Phunkafizer/OT-Thing/Firmware/include/sensors.h

#pragma once

#include <Arduino.h>
#include <ArduinoJson.h>
#include <AsyncTCP.h>
#include <OneWire.h>
#include <NimBLEDevice.h>
#include <vector>
#include "util.h"

class AddressableSensor {
friend class Sensor;
friend class SensorLock;
private:
    uint8_t adrLen;
    static SemaphoreHandle_t mutex;
protected:
    AddressableSensor(const uint8_t *adr, const uint8_t adrLen, AddressableSensor **prev);
    String getAdr() const;
    static AddressableSensor* find(String adr, AddressableSensor *last);
    static void writeJsonAll(JsonObject &status, AddressableSensor *last);
    virtual void writeJson(JsonVariant val) = 0;
    static bool sendDiscoveryAll(AddressableSensor *last);
    virtual bool sendDiscovery() = 0;
    uint8_t adr[8];
    AddressableSensor *next;
    double temp;
public:
    static void begin();
};

class BLESensor: public AddressableSensor {
private:
    void parse(std::string &data);
    static BLESensor *last;
    uint8_t rh;
    uint8_t bat;
    int8_t rssi;
protected:
    void writeJson(JsonVariant val) override;
    bool sendDiscovery() override;
public:
    BLESensor(const uint8_t *adr);
    static void begin();
    static void onDiscovery(const NimBLEAdvertisedDevice* dev);
    static void writeJsonAll(JsonObject &status);
    static BLESensor* find(const uint8_t *adr);
    static bool sendDiscoveryAll();
};

class OneWireNode: public AddressableSensor {
private:
    static OneWireNode *last;
protected:
    void writeJson(JsonVariant val) override;
    bool sendDiscovery() override;
public:
    OneWireNode(uint8_t *addr);
    virtual ~OneWireNode() {}
    static void begin(const uint8_t gpio);
    static void clear();
    static OneWireNode* find(String adr);
    static void loop();
    static void writeJsonAll(JsonObject &status);
    static bool sendDiscoveryAll();
};

class Sensor {
public:
    enum Source: int8_t {
        SOURCE_SCHED = -3,
        SOURCE_HTTP = -2,
        SOURCE_NA = -1,
        SOURCE_MQTT = 0,
        SOURCE_OT = 1,
        SOURCE_BLE = 2,
        SOURCE_1WIRE = 3,
        SOURCE_OPENWEATHER = 4,
        SOURCE_AUTO = 5 // has to be last item in this list!
    };
    Source lastSetSrc {SOURCE_NA};
    OneWireNode *own; // points to a OneWireNode if configured
    Sensor(const double alpha);
    virtual void set(const double val, const Source src, const Source lastSrc = SOURCE_NA);
    bool get(double &val, const bool raw = false);
    virtual void writeJson(JsonVariant val);
    virtual void setConfig(JsonObject &obj);
    bool isMqttSource();
    bool isOtSource();
    static void loopAll();
    explicit operator bool() const;
    static std::vector<Sensor*> findByOwn(const OneWireNode *own);
protected:
    Source src;
    double value;
    double smoothed;
    bool setFlag;
    virtual void loop() {}
private:
    void updateSmooth();
    static uint32_t lastSmooth;
    static Sensor *lastSensor;
    Sensor *prevSensor;
    uint8_t adr[6];
    double alpha;
};

class AutoSensor: public Sensor {
public:
    AutoSensor();
    void set(const double val, const Source src, const Source lastSrc = SOURCE_NA) override;
private:
    double values[SOURCE_AUTO + 1];
};

class OutsideTemp: public Sensor {
public:
    String owResult;
    OutsideTemp();
    void setConfig(JsonObject &obj) override;
    void set(const double val, const Source src, const Source lastSrc = SOURCE_NA) override;
    void writeJson(JsonVariant val) override;
    double getAvg() const;
protected:
    void loop() override;
private:
    uint32_t nextMillis;
    uint32_t interval;
    double lat, lon;
    String apikey;
    AsyncClient acli;
    String replyBuf;
    enum {
        HTTP_IDLE,
        HTTP_CONNECTING,
        HTTP_RECEIVING
    } httpState;
    double minValues[24];
    double maxValues[24];
    int lastHistPos {-1};
};

extern Sensor roomTemp[2];
extern AutoSensor roomSetPoint[2];
extern OutsideTemp outsideTemp;
extern Sensor returnTemp[2];
