Phunkafizer/OT-Thing/Firmware/src/mqtt.cpp

#include "mqtt.h"
#include <WiFi.h>
#include <devstatus.h>
#include "portal.h"
#include "sensors.h"
#include "hwdef.h"
#include "auxInput.h"
#include "otcontrol.h"
#include "util.h"

static struct {
    Mqtt::MqttTopic topic;
    const char *str;
} topicList[] PROGMEM = {
    {Mqtt::TOPIC_OUTSIDETEMP, "outsideTemp"},
    {Mqtt::TOPIC_DHWSETTEMP, "dhwSetTemp"},
    {Mqtt::TOPIC_CHSETTEMP1, "chSetTemp1"},
    {Mqtt::TOPIC_CHSETTEMP2, "chSetTemp2"},
    {Mqtt::TOPIC_CHMINTEMP1, "chMinTemp1"},
    {Mqtt::TOPIC_CHMINTEMP2, "chMinTemp2"},
    {Mqtt::TOPIC_DHWMODE, "dhwMode"},
    {Mqtt::TOPIC_CHMODE1, "chMode1"},
    {Mqtt::TOPIC_CHMODE2, "chMode2"},
    {Mqtt::TOPIC_ROOMTEMP1, "roomTemp1"},
    {Mqtt::TOPIC_ROOMTEMP2, "roomTemp2"},
    {Mqtt::TOPIC_ROOMMODE1, "roomMode1"},
    {Mqtt::TOPIC_ROOMMODE2, "roomMode2"},
    {Mqtt::TOPIC_ROOMSETPOINT1, "roomSetpoint1"},
    {Mqtt::TOPIC_ROOMSETPOINT2, "roomSetpoint2"},
    {Mqtt::TOPIC_OVERRIDECHFLOW1, "overrideChFlow1"},
    {Mqtt::TOPIC_OVERRIDECHFLOW2, "overrideChFlow2"},
    {Mqtt::TOPIC_OVERRIDECHON1, "overrideChOn1"},
    {Mqtt::TOPIC_OVERRIDECHON2, "overrideChOn2"},
    {Mqtt::TOPIC_VENTSETPOINT, "ventSetpoint"},
    {Mqtt::TOPIC_VENTENABLE, "ventEnable"},
    {Mqtt::TOPIC_OPENBYPASS, "openBypass"},
    {Mqtt::TOPIC_AUTOBYPASS, "autoBypass"},
    {Mqtt::TOPIC_FREEVENTENABLE, "freeVentEnable"},
    {Mqtt::TOPIC_MAXMODULATION, "maxModulation"},
    {Mqtt::TOPIC_BYPASS, "bypass"},
    {Mqtt::TOPIC_SUMMERMODE, "summerMode"},
    {Mqtt::TOPIC_DHWBLOCKING, "dhwBlocking"},
    {Mqtt::TOPIC_COOLINGMODE, "coolingMode"},
    {Mqtt::TOPIC_COOLINGCTRL, "coolingCtrl"},
    {Mqtt::TOPIC_TURBOSHIFT1, "turboShift1"},
    {Mqtt::TOPIC_TURBOSHIFT2, "turboShift2"},
    {Mqtt::TOPIC_TURBODURATION1, "turboDuration1"},
    {Mqtt::TOPIC_TURBODURATION2, "turboDuration2"},
};

Mqtt mqtt;
static uint32_t numDisc = 0;
static WiFiClient espClient;
static String mqttRxTopic;
static String mqttRxPayload;

void mqttConnectCb(bool sessionPresent) {
    mqtt.onConnect();
}

void mqttDisconnectCb(AsyncMqttClientDisconnectReason reason) {
    mqtt.onDisconnect(reason);
}

static void mqttMessageReceived(char* topic, char* payload, AsyncMqttClientMessageProperties properties, size_t len, size_t index, size_t total) {
    // AsyncMqttClient may deliver one MQTT message in multiple chunks.
    if (index == 0) {
        mqttRxTopic = String(topic);
        mqttRxPayload = "";
        mqttRxPayload.reserve(total);
    }

    if (mqttRxTopic != String(topic)) {
        mqttRxTopic = String(topic);
        mqttRxPayload = "";
        mqttRxPayload.reserve(total);
    }

    mqttRxPayload.concat(payload, len);

    if ((index + len) >= total) {
        mqtt.onMessage(topic, mqttRxPayload);
        mqttRxTopic = "";
        mqttRxPayload = "";
    }
}

Mqtt::Mqtt():
        lastConTry(0),
        lastStatus(0),
        configSet(false),
        conFlag(false),
        lastSentStatus(0) {
    cli.onConnect(mqttConnectCb);
    cli.onDisconnect(mqttDisconnectCb);
    cli.onMessage(mqttMessageReceived);
}

void Mqtt::begin() {
    String shortMac = getShortMac();
    baseTopic = F("otthing/");
    baseTopic += shortMac;
    statusTopic = baseTopic + F("/status");
}

void Mqtt::onConnect() {
    portal.textAll(F("MQTT connected"));

    String topic = baseTopic + F("/+/set");
    cli.subscribe(topic.c_str(), 0);

    discFlag = false;
    conFlag = true;
}

void Mqtt::onDisconnect(AsyncMqttClientDisconnectReason reason) {
    if (conFlag) {
        String msg = F("MQTT disconnected ");
        msg += String((int) reason);
        portal.textAll(msg);
        conFlag = false;
        numDisc++;
    }
}

bool Mqtt::connected() {
    return cli.connected();
}

void Mqtt::setConfig(const MqttConfig conf) {
    lastConTry = millis() - 8000;
    cli.disconnect(false);
    config = conf;
    cli.setServer(config.host.c_str(), conf.port);
    cli.setKeepAlive(config.keepAlive);
    cli.setCredentials(config.user.c_str(), config.pass.c_str());
    configSet = !conf.host.isEmpty();
    numDisc = 0;
}

uint32_t Mqtt::getNumDisc() const {
    return numDisc;
}

String Mqtt::getCmdTopic(const MqttTopic topic) {
    String result = baseTopic + '/';
    result += getTopicString(topic);
    result += "/set";
    return result;
}

String Mqtt::getBaseTopic() {
    return baseTopic;
}

void Mqtt::loop() {
    if (!cli.connected() && ((millis() - lastConTry) > 10000) && WiFi.isConnected() && configSet) {
        lastConTry = millis();
        haDisc.defaultStateTopic = baseTopic + F("/state");
        cli.setWill(statusTopic.c_str(), 0, true, "0");
        lastSentStatus = 0;
        cli.connect();        
    }

    if (cli.connected()) {
        if (!discFlag) {
            discFlag = true;
            discFlag &= otcontrol.sendDiscovery();
            discFlag &= OneWireNode::sendDiscoveryAll();
            discFlag &= BLESensor::sendDiscoveryAll();
            for (int i=0; i<sizeof(auxInput) / sizeof(auxInput[0]); i++)
                discFlag &= auxInput[i].sendDiscovery();
        }

        int newStatus = 1 << 0;
        if (otcontrol.masterConnected())
            newStatus |= 1 << 1;
        if (otcontrol.slaveConnected())
            newStatus |= 1 << 2;
        if (newStatus != lastSentStatus) {
            lastSentStatus = newStatus;
            cli.publish(statusTopic.c_str(), 0, true, String(newStatus).c_str());
        }

        if ((millis() - lastStatus) > 5000) {
            lastStatus = millis();
            JsonDocument doc;
            JsonObject jobj = doc.to<JsonObject>();
            devstatus.buildDoc(jobj);
            String statStr;
            serializeJson(jobj, statStr);
            cli.publish(haDisc.defaultStateTopic.c_str(), 0, false, statStr.c_str());
        }
    }
}

bool Mqtt::strToBool(const String &str) {
    return str.compareTo(F("ON")) == 0;
}

bool Mqtt::publish(String topic, JsonDocument &payload, const bool retain) {
    if (!cli.connected())
        return false;

    String ps;
    if (!payload.isNull())
        serializeJson(payload, ps);
    cli.publish(topic.c_str(), 0, retain, ps.c_str());
    return true;
}

void Mqtt::onMessage(const char *topic, String &payload) {
    String topicStr = topic;
    topicStr.remove(0, baseTopic.length() + 1);
    topicStr.remove(topicStr.length() - 4, 4); // remove "/set" from end of topic

    String log = F("MQTT: ");
    log += topic;
    log += " ";
    log += payload;
    portal.textAll(log);

    if (setValue(topicStr, payload)) {
        if ((millis() - lastStatus) < 4500)
            lastStatus = millis() - 4500;
    }
}

bool Mqtt::setValue(const String &key, const String &value, const bool viaHttp) {
    enum MqttTopic etop = TOPIC_UNKNOWN;
    for (int i=0; i<sizeof(topicList) / sizeof(topicList[0]); i++)
        if (key.compareTo(FPSTR(topicList[i].str)) == 0) {
            etop = topicList[i].topic;
            break;
        }

    const Sensor::Source lastSrc = viaHttp ? Sensor::SOURCE_HTTP : Sensor::SOURCE_MQTT;
    bool retain = true;

    switch (etop) {
    case TOPIC_UNKNOWN: {
        String log = F("MQTT unknown topic: ");
        log += key;
        portal.textAll(log);
        return false;
    }

    case TOPIC_OUTSIDETEMP: {
        double d = value.toFloat();
        outsideTemp.set(d, Sensor::SOURCE_MQTT, lastSrc);
        break;
    }

    case TOPIC_DHWSETTEMP: {
        double d = value.toFloat();
        otcontrol.dhwControl.setSetpoint(d, lastSrc);
        break;
    }   

    case TOPIC_DHWMODE: {
        auto mode = haDisc.strToClimateMode(value);
        if (mode != HADiscovery::MODE_UNKNOWN)
            otcontrol.setDhwCtrlMode(mode);
        break;
    }

    case TOPIC_CHSETTEMP1:
    case TOPIC_CHSETTEMP2: {
        double d = value.toFloat();
        otcontrol.setChTemp(d, (uint8_t) (etop - TOPIC_CHSETTEMP1), lastSrc);
        break;
    }

    case TOPIC_CHMINTEMP1:
    case TOPIC_CHMINTEMP2: {
        double d = value.toFloat();
        otcontrol.setFlowMin(d, (uint8_t) (etop - TOPIC_CHMINTEMP1));
        break;
    }

    case TOPIC_CHMODE1:
    case TOPIC_CHMODE2: {
        const uint8_t ch = (uint8_t) (etop - TOPIC_CHMODE1);
        auto mode = haDisc.strToClimateMode(value);
        if (mode != HADiscovery::MODE_UNKNOWN)
            otcontrol.setChCtrlMode(mode, ch);
        break;
    }

    case TOPIC_ROOMTEMP1:
    case TOPIC_ROOMTEMP2: {
        const uint8_t ch = (uint8_t) (etop - TOPIC_ROOMTEMP1);
        double d = value.toFloat();
        roomTemp[ch].set(d, Sensor::SOURCE_MQTT, lastSrc);
        otcontrol.forceFlowCalc(ch);
        break;
    }

    case TOPIC_ROOMSETPOINT1:
    case TOPIC_ROOMSETPOINT2: {
        const uint8_t ch = (uint8_t) (etop - TOPIC_ROOMSETPOINT1);
        double d = value.toFloat();
        roomSetPoint[ch].set(d, Sensor::SOURCE_MQTT, lastSrc);
        otcontrol.forceFlowCalc(ch);
        break;
    }

    case TOPIC_ROOMMODE1:
    case TOPIC_ROOMMODE2: {
        auto mode = haDisc.strToClimateMode(value);
        if (mode != HADiscovery::MODE_UNKNOWN)
            otcontrol.setRoomMode(mode, (uint8_t) (etop - TOPIC_ROOMMODE1));
        break;
    }

    case TOPIC_OVERRIDECHON1:
    case TOPIC_OVERRIDECHON2:
        otcontrol.setOverrideChOn(strToBool(value), (uint8_t) (etop - TOPIC_OVERRIDECHON1));
        break;

    case TOPIC_OVERRIDECHFLOW1:
    case TOPIC_OVERRIDECHFLOW2:
        otcontrol.setOverrideChFlow(strToBool(value), (uint8_t) (etop - TOPIC_OVERRIDECHFLOW1));
        break;

    case TOPIC_VENTSETPOINT: {
        uint8_t val = value.toInt();
        otcontrol.ventCtrl.setVentSetpoint(val);
        break;
    }

    case TOPIC_VENTENABLE:
        otcontrol.ventCtrl.setVentEnable(strToBool(value));
        break;

    case TOPIC_OPENBYPASS:
        otcontrol.ventCtrl.setOpenBypass(strToBool(value));
        break;

    case TOPIC_AUTOBYPASS:
        otcontrol.ventCtrl.setAutoBypass(strToBool(value));
        break;

    case TOPIC_FREEVENTENABLE:
        otcontrol.ventCtrl.setFreeVentEnable(strToBool(value));
        break;

    case TOPIC_MAXMODULATION: {
        int i = value.toInt();
        otcontrol.setMaxMod(i);
        break;
    }

    case TOPIC_BYPASS:
        otcontrol.setBypass(strToBool(value));
        break;

    case TOPIC_SUMMERMODE:
        otcontrol.setSummerMode(strToBool(value));
        break;

    case TOPIC_DHWBLOCKING:
        otcontrol.setDhwBlocking(strToBool(value));
        break;

    case TOPIC_COOLINGMODE:
        otcontrol.setCoolingMode(strToBool(value));
        break;

    case TOPIC_COOLINGCTRL:
        otcontrol.setCoolingCtrl(value.toInt());
        break;

    case TOPIC_TURBOSHIFT1:
    case TOPIC_TURBOSHIFT2: {
        const uint8_t ch = (uint8_t) (etop - TOPIC_TURBOSHIFT1);
        double d = value.toFloat();
        otcontrol.setTurboShift(d, ch);
        retain = false;
        break;
    }

    case TOPIC_TURBODURATION1:
    case TOPIC_TURBODURATION2: {
        const uint8_t ch = (uint8_t) (etop - TOPIC_TURBODURATION1);
        uint32_t d = value.toInt();
        otcontrol.setTurboDuration(d, ch);
        retain = false;
        break;
    }

    default:
        return false;
    }

    if (viaHttp)
        sendValue(etop, value, retain);

    return true;
}

void Mqtt::sendValue(const MqttTopic topic, const String &value, const bool retain) {
    if (!connected())
        return;

    String topicStr = baseTopic + '/';
    topicStr += getTopicString(topic);
    topicStr += "/set";
    cli.publish(topicStr.c_str(), 0, retain, value.c_str());
}

String Mqtt::getTopicString(const MqttTopic topic) {
    for (int i=0; i<sizeof(topicList) / sizeof(topicList[0]); i++)
        if (topicList[i].topic == topic)
            return FPSTR(topicList[i].str);
    return "";
}

String Mqtt::getValuePath(const ValueTemplateType vt, PGM_P field, const uint8_t ch, const uint8_t ommit) {
    String result = F("{% set tmp=(((value_json");
    String ftmp = FPSTR(field); // e. g. "dhw_set_t", "status.dhw_enable"

    switch (vt) {
    case VALTMPL_NONE:
        return "";
        
    case VALTMPL_ROOT:
        result += F(")"); // result: {% set tmp=(((value_json)
        break;
        
    case VALTMPL_SLAVE:
        result += F(".get('slave') or {})"); // result: {% set tmp=(((value_json.get('slave') or {})
        break;

    case VALTMPL_MASTER: {
        const int pidx = ftmp.indexOf('.');
        if (pidx > -1)
            ftmp = ftmp.substring(0, pidx) + F(".data") + ftmp.substring(pidx); // adds 
        else
            ftmp += F(".data");
        [[fallthrough]];
    }

    case VALTMPL_MASTER_ROOT:
        result += F(".get('master') or {})"); // result: {% set tmp=(((value_json.get('master') or {})
        break;

    case VALTMPL_ROOMUNIT: {
        const int pidx = ftmp.indexOf('.');
        if (pidx > -1)
            ftmp = ftmp.substring(0, pidx) + F(".data") + ftmp.substring(pidx);
        else
            ftmp += F(".data");
        [[fallthrough]];
    }

    case VALTMPL_ROOMUNIT_ROOT:
        result += F(".get('roomunit') or {})");
        break;

    case VALTMPL_HEATING_CIRCUIT:
        result += F(".get('heatercircuit') or [])[#]");
        break;

    case VALTMPL_DHW:
        result += F(".get('dhw') or {})");
        break;

    case VALTMPL_FLAMESTATS:
        result += F(".get('slave') or {}).get('flameStats') or {}");
        break;

    case VALTMPL_COOLING:
        result += F(".get('cooling') or {})");
        break;

    case VALTMPL_VENT:
        result += F(".get('vent') or {})");
        break;
    }

    int numbrak = 2;

    while (true) {
        auto pidx = ftmp.indexOf('.');

        if (pidx > -1) {
            result += F(".get('");
            result += ftmp.substring(0, pidx);
            result += F("') or {})");
            ftmp.remove(0, pidx + 1);
            numbrak--;
        }
        else
            break;
    }
    for (int i=0; i<numbrak; i++)
        result += ')';

    result += F(".get('");
    result += ftmp;
    result += F("') %}");

    if (ch == ommit)
        result.replace("#", "");
    else
        result.replace("#", String(ch));

    return result;
}

String Mqtt::getValueTemplate(const ValueTemplateType vt, PGM_P field, const uint8_t ch, const uint8_t ommit) {
    String result = getValuePath(vt, field, ch, ommit);
    result += F("{{ tmp | default(none) }}");
    return result;
}

String Mqtt::getValueTemplateBool(const ValueTemplateType vt, PGM_P field, const uint8_t ch, const uint8_t ommit) {
    String result = getValuePath(vt, field, ch, ommit);
    result += F("{{ none if tmp is none else 'ON' if tmp else 'OFF' }}");
    return result;
}

String &Mqtt::getStatusTopic() {
    return statusTopic;
}
