Phunkafizer/OT-Thing/Firmware/include/mqtt.h

#pragma once

#include <AsyncMqttClient.h>
#include <ArduinoJson.h>

struct MqttConfig {
    String host;
    uint16_t port;
    bool tls;
    String user;
    String pass;
    uint16_t keepAlive;
};

class Mqtt {
public:
    enum MqttTopic: uint8_t {
        TOPIC_OUTSIDETEMP,
        TOPIC_DHWSETTEMP,
        TOPIC_CHSETTEMP1,
        TOPIC_CHSETTEMP2,
        TOPIC_CHMINTEMP1,
        TOPIC_CHMINTEMP2,
        TOPIC_DHWMODE,
        TOPIC_CHMODE1,
        TOPIC_CHMODE2,
        TOPIC_ROOMTEMP1,
        TOPIC_ROOMTEMP2,
        TOPIC_ROOMSETPOINT1,
        TOPIC_ROOMSETPOINT2,
        TOPIC_ROOMMODE1,
        TOPIC_ROOMMODE2,
        TOPIC_OVERRIDECHON1,
        TOPIC_OVERRIDECHON2,
        TOPIC_OVERRIDECHFLOW1,
        TOPIC_OVERRIDECHFLOW2,
        TOPIC_VENTSETPOINT,
        TOPIC_VENTENABLE,
        TOPIC_OPENBYPASS,
        TOPIC_AUTOBYPASS,
        TOPIC_FREEVENTENABLE,
        TOPIC_MAXMODULATION,
        TOPIC_BYPASS,
        TOPIC_SUMMERMODE,
        TOPIC_DHWBLOCKING,
        TOPIC_COOLINGMODE,
        TOPIC_COOLINGCTRL,
        TOPIC_TURBOSHIFT1,
        TOPIC_TURBOSHIFT2,
        TOPIC_TURBODURATION1,
        TOPIC_TURBODURATION2,
        TOPIC_UNKNOWN // has to be at end of list!
    };
    enum ValueTemplateType: int8_t {
        VALTMPL_NONE = -1,
        VALTMPL_ROOT,
        VALTMPL_DHW,
        VALTMPL_SLAVE,
        VALTMPL_MASTER,
        VALTMPL_MASTER_ROOT,
        VALTMPL_ROOMUNIT,
        VALTMPL_ROOMUNIT_ROOT,
        VALTMPL_HEATING_CIRCUIT,
        VALTMPL_FLAMESTATS,
        VALTMPL_COOLING,
        VALTMPL_VENT
    };
    Mqtt();
    void begin();
    void loop();
    bool connected();
    void setConfig(const MqttConfig conf);
    bool publish(String topic, JsonDocument &payload, const bool retain);
    void onMessage(const char *topic, String &payload);
    bool setValue(const String &key, const String &value, const bool viaHttp = false);
    void sendValue(const MqttTopic topic, const String &value, const bool retain = true);
    String getBaseTopic();
    static String getTopicString(const MqttTopic topic);
    String getCmdTopic(const MqttTopic topic);
    uint32_t getNumDisc() const;
    String getValueTemplate(const ValueTemplateType vt, PGM_P field, const uint8_t ch=-1, const uint8_t ommit=-1);
    String getValueTemplateBool(const ValueTemplateType vt, PGM_P field, const uint8_t ch=-1, const uint8_t ommit=-1);
    String &getStatusTopic();
private:
    void onConnect();
    void onDisconnect(AsyncMqttClientDisconnectReason reason);
    friend void mqttConnectCb(bool sessionPresent);
    friend void mqttDisconnectCb(AsyncMqttClientDisconnectReason reason);
    bool strToBool(const String &str);
    String getValuePath(const ValueTemplateType vt, PGM_P field, const uint8_t ch, const uint8_t ommit);
    AsyncMqttClient cli;
    uint32_t lastConTry;
    uint32_t lastStatus;
    MqttConfig config;
    bool configSet;
    String baseTopic;
    String statusTopic;
    bool discFlag {false}; // discovery flag; set after MQTT (re-) connect
    bool conFlag;
    int lastSentStatus;
    
};

extern Mqtt mqtt;
