Phunkafizer/OT-Thing/Firmware/src/flamestats.cpp

#include "flamestats.h"
#include "otcontrol.h"
#include "devstatus.h"

FlameStats flameStats;

bool FlameStats::currentFlame {false};

void FlameStats::flameChange(const bool flame) {
    if (lastLoop == 0) {
        // this is first flame on within 1st minute
        memset(on.buf, 60, sizeof(on.buf));
        on.sum = BUFSIZE_MINUTES * 60UL;
    }

    if (flame) {
        cycles.current++;
        offTimes.current = (millis() - lastEdge) / 1000;
        if ((lastEdge > 0) && !offTimesInit) {
            // this is first flame on after 1st flame off, initialize off times buffer
            for (int i=0; i<BUFSIZE_CYCLES; i++)
                offTimes.buf[i] = offTimes.current;
            offTimes.sum = offTimes.current * BUFSIZE_CYCLES;
            offTimesInit = true;
        }
        offTimes.update(idxCycles);
    }
    else {
        onTimes.current = (millis() - lastEdge) / 1000;
        if ((lastEdge > 0) && !onTimesInit) {
            // this is first flame off after 1st flame on, initialize on times buffer
            for (int i=0; i<BUFSIZE_CYCLES; i++)
                onTimes.buf[i] = onTimes.current;
            onTimes.sum = onTimes.current * BUFSIZE_CYCLES;
            onTimesInit = true;
        }
        onTimes.update(idxCycles);
        idxCycles = (idxCycles + 1) % BUFSIZE_CYCLES;
    }
    
    update();
    lastEdge = millis();
}

void FlameStats::update() {
    if (currentFlame) {
        uint8_t diff = 0;
        if (lastEdge > lastLoop)
            diff = (millis() - lastEdge) / 1000;
        else
            diff = (millis() - lastLoop) / 1000;
        on.current += diff;
    }
}

double FlameStats::secToMin(const uint32_t sec) const {
    return round(sec * 10.0 / 60.0) / 10.0;
}

uint8_t FlameStats::getDuty() const {
    return 100 * on.sum / BUFSIZE_MINUTES / 60;
}

double FlameStats::getFreq() const {
    return round(cycles.sum / (BUFSIZE_MINUTES / 60.0) * 10) / 10.0;
}

/*
 * @brief return current on-time / seconds, 0 if flame is off
 */
int FlameStats::getCurrentOnTime() const {
    if (!currentFlame)
        return 0;
    return (millis() - lastEdge) / 1000;
}

/* 
 * @brief return average on-time over last x on/off cycles / minutes
 */

double FlameStats::getOnTime() const {
    return secToMin(onTimes.sum / BUFSIZE_CYCLES);
}

/* 
 * @brief return average off-time over last x on/off cycles / minutes
 */

double FlameStats::getOffTime() const {
    return secToMin(offTimes.sum / BUFSIZE_CYCLES);
}

void FlameStats::loop() {
    if (millis() >= lastLoop + 60000) {
        update();

        on.update(idxMinutes);
        cycles.update(idxMinutes);
        
        idxMinutes = (idxMinutes + 1) % BUFSIZE_MINUTES;
        lastLoop = millis();
    }
}

template <typename T1, size_t T2>
void FlameStats::Ringbuf<T1, T2>::update(const uint8_t idx) {
    sum -= buf[idx]; // remove old value
    buf[idx] = current;
    sum += current;
    current = 0;
}

void FlameStats::writeJson(JsonObject &obj) const {
    JsonObject fs = obj[FPSTR(STR_STATKEY_FLAMESTATS)].to<JsonObject>();
    fs[FPSTR(STR_STATKEY_FLAMESTATS_DUTY)] = getDuty();
    fs[FPSTR(STR_STATKEY_FLAMESTATS_FREQ)] = getFreq();
    if (onTimesInit) {
        fs[FPSTR(STR_STATKEY_FLAMESTATS_ONTIME)] = getOnTime();
        double lasttOnTime = onTimes.buf[(idxCycles + BUFSIZE_CYCLES - 1) % BUFSIZE_CYCLES];
        fs[FPSTR(STR_STATKEY_FLAMESTATS_LASTONTIME)] = secToMin(lasttOnTime);
    }
    if (offTimesInit)
        fs[FPSTR(STR_STATKEY_FLAMESTATS_OFFTIME)] = getOffTime();
    if (currentFlame)
        fs[FPSTR(STR_STATKEY_FLAMESTATS_CURRENTONTIME)] = secToMin(getCurrentOnTime());
}
